Riconec/iCE40-feather/gateware/snake/snake.v

// -----------------------------------------------------------------------------
// Copyright (c) 2019 All rights reserved
// -----------------------------------------------------------------------------
// Author      : Josh Johnson <josh@joshajohnson.com>
// File        : snake.v
// Description : WIP game of snake of the LED matrix FeatherWing
// Created     : 2019-09-06 19:22:27
// Revised     : 2019-09-06 19:22:27
// Editor      : sublime text3, tab size (4)
// -----------------------------------------------------------------------------

`default_nettype none
`include "../src/debounce.v"
`include "../src/ledMatrix.v"

module top(
    input clk,
    input btn_up,
    input btn_left,
    input btn_right,
    input btn_down,
    output wire [5:0] row,
    output wire [5:0] col
);

	wire btn_up_rising, btn_left_rising, btn_right_rising, btn_down_rising;
	reg error = 0;
	reg reset_game = 1;
	reg clk_1Hz_rst = 0;

	// Matrix dimensions
	parameter DIM_X = 6;
	parameter DIM_Y = 6;

	// Mode State Machine
	parameter IDLE 	= 4'b0000;
	parameter BEGIN = 4'b0010;
	parameter PLAY 	= 4'b0100;
	parameter END 	= 4'b1000;

	reg [3:0] state = IDLE;
	reg [3:0] next_state;

	// Display control
	reg [3:0] display = 0;
	reg [2:0] countdown = 0;

	parameter START	= 4'b0000;
	parameter ONE	= 4'b0001;
	parameter TWO	= 4'b0010;
	parameter THREE	= 4'b0011;
	parameter GAME 	= 4'b0100;
	parameter DEAD 	= 4'b1000;

	// Drive state machine
	always @(*) begin
		state <= next_state;
	end

	// Mode state machine
	always @(posedge clk) begin
		case (state)
			IDLE : begin
				// Move to begin once a key is pressed
				display <= START;
				reset_game <= 0;
				clk_1Hz_rst <= 1;
				if (btn_up_rising || btn_right_rising || btn_left_rising || btn_down_rising) begin
					next_state = BEGIN;
					countdown <= 3;
				end
			end

			BEGIN : begin
				// Display 3,2,1 on screen before beginning game
				clk_1Hz_rst <= 0;
				display <= countdown;
				if (pulse_1Hz) begin
					countdown <= countdown - 1;
				end

				if (countdown == 0) begin
					next_state <= PLAY;
				end
			end

			PLAY : begin
				// Play snake util it ends
				display <= GAME;
				if (error) begin
					next_state <= END;
				end
			end

			END : begin
				// Display sad face until button pressed 
				display <= DEAD;
				if (btn_up_rising || btn_left_rising || btn_right_rising || btn_down_rising) begin
					next_state <= IDLE;
					reset_game <= 1;
				end
			end

			default: next_state <= IDLE;
		endcase
	end

	// Direction of snake
	parameter UP = 	4'b0001;
	parameter DOWN = 4'b0010;
	parameter LEFT = 4'b0100;
	parameter RIGHT = 4'b1000;

	// Initial direction of snake
	reg [3:0] direction = UP;

	// Position
	reg [2:0] pos_x = 0;
	reg [2:0] pos_y = 0;

	// Change direction after button press
	always @(posedge clk) begin
		if (reset_game) begin
			direction <= UP;
		end else if (btn_up_rising) begin
				direction <= UP;
		end else if (btn_left_rising) begin
				direction <= LEFT;
		end else if (btn_right_rising) begin
				direction <= RIGHT;
		end else if (btn_down_rising) begin
				direction <= DOWN;
		end 
	end

	// Move snake every clock cycle only if playing snake
	wire pulse_1Hz;
	always @(posedge clk) begin
		if (reset_game) begin
			error <= 1'b0;
			pos_x <= 1'b0;
			pos_y <= 1'b0;
		end else if (pulse_1Hz && (state == PLAY)) begin
			case(direction)
			UP: 	if (pos_y < DIM_Y) begin
						if (pos_y < DIM_Y - 1) begin
							pos_y <= pos_y + 1;
							error <= 1'b0;
						end else begin
							error <= 1'b1;
						end
					end 

			LEFT: 	if (pos_x >= 0) begin
						if (pos_x > 0) begin
							pos_x <= pos_x - 1;
							error <= 1'b0;
				  		end else begin
				  			error <= 1'b1;
				  		end

				  	end 

			RIGHT: 	if (pos_x < DIM_X) begin
						if (pos_x < DIM_X - 1) begin
							pos_x <= pos_x + 1;
							error <= 1'b0;
						end else begin
							error <= 1'b1;
						end
					end

			DOWN: 	if (pos_y >= 0) begin
						if (pos_y > 0) begin
							pos_y <= pos_y - 1;
							error <= 1'b0;
				  		end else begin
				  			error <= 1'b1;
				  		end

				  	end 

			default: pos_x = pos_x;
			endcase
		end
	end

	// Display image on screen
	reg [35:0] img;
	always @(posedge clk) begin
		case (display)
			START :	begin
					img [5:0] 		= 6'b000000;
					img [11:6] 		= 6'b010010;
					img [17:12] 	= 6'b000000;
					img [23:18] 	= 6'b100001;
					img [29:24] 	= 6'b011110;
					img [35:30] 	= 6'b000000;
			end 

			ONE : 	begin
					img [5:0] 		= 6'b000000;
					img [11:6] 		= 6'b011100;
					img [17:12] 	= 6'b000100;
					img [23:18] 	= 6'b000100;
					img [29:24] 	= 6'b000100;
					img [35:30] 	= 6'b011110;
			end

			TWO : 	begin
					img [5:0] 		= 6'b111100;
					img [11:6] 		= 6'b000010;
					img [17:12] 	= 6'b011100;
					img [23:18] 	= 6'b100000;
					img [29:24] 	= 6'b100000;
					img [35:30] 	= 6'b011110;
			end

			THREE : begin
					img [5:0] 		= 6'b011110;
					img [11:6] 		= 6'b000010;
					img [17:12] 	= 6'b011110;
					img [23:18] 	= 6'b000010;
					img [29:24] 	= 6'b000010;
					img [35:30] 	= 6'b011110;
			end

			GAME : begin
				img = 0;
				case (5 - pos_y)
					3'd0: img [5:0] 	= 1 << (5 - pos_x);
					3'd1: img [11:6] 	= 1 << (5 - pos_x);
					3'd2: img [17:12] 	= 1 << (5 - pos_x);
					3'd3: img [23:18] 	= 1 << (5 - pos_x);
					3'd4: img [29:24] 	= 1 << (5 - pos_x);
					3'd5: img [35:30] 	= 1 << (5 - pos_x);
					default: img 		= 36'd0;
				endcase
				end

			DEAD : begin
					img [5:0] 		= 6'b000000;
					img [11:6] 		= 6'b010010;
					img [17:12] 	= 6'b000000;
					img [23:18] 	= 6'b000000;
					img [29:24] 	= 6'b011110;
					img [35:30] 	= 6'b000000;
			end
			default : begin
					img [5:0] 		= 6'b000000;
					img [11:6] 		= 6'b000000;
					img [17:12] 	= 6'b000000;
					img [23:18] 	= 6'b000000;
					img [29:24] 	= 6'b000000;
					img [35:30] 	= 6'b000000;
			end 
		endcase
	end

	// Drive matrix
	ledMatrix inst_ledMatrix (
		.clk	(clk), 
		.img	(img), 
		.row 	(row), 
		.col 	(col)
	);

`ifdef SIMULATION
	// Increase the 1Hz clock speed
	clkDivHz #(
		.FREQUENCY(100)
	) inst_clkDivHz (
		.clk          (clk),
		.rst          (clk_1Hz_rst),
		.enable       (1'b1),
		.dividedClk   (),
		.dividedPulse (pulse_1Hz)
	);

	// pass buttons through without debounce
	assign btn_up_rising = btn_up;
	assign btn_down_rising = btn_down;
	assign btn_right_rising = btn_right;
	assign btn_left_rising = btn_left;

`else
	// 1Hz clock
	clkDivHz #(
		.FREQUENCY(1)
	) inst_clkDivHz (
		.clk          (clk),
		.rst          (clk_1Hz_rst),
		.enable       (1'b1),
		.dividedClk   (),
		.dividedPulse (pulse_1Hz)
	);

	// debonce buttons
	debounce debounce_up
	(
		.clk            (clk),
		.button         (btn_up),
		.button_db      (),
		.button_rising  (btn_up_rising),
		.button_falling ()
	);

	debounce debounce_left
	(
		.clk            (clk),
		.button         (btn_left),
		.button_db      (),
		.button_rising  (btn_left_rising),
		.button_falling ()
	);

	debounce debounce_right
	(
		.clk            (clk),
		.button         (btn_right),
		.button_db      (),
		.button_rising  (btn_right_rising),
		.button_falling ()
	);

	debounce debounce_down
	(
		.clk            (clk),
		.button         (btn_down),
		.button_db      (),
		.button_rising  (btn_down_rising),
		.button_falling ()
	);
`endif
endmodule
