Riconec/iCE40-feather/gateware/debounce/debounce.v

// Debounces an active high button, using a shift register approach. 
// This results in ~50ms of latency which is unperceivable to almost everyone.
// @input button: button to be debounced
// @output button_db: debounced button
// @output button_rising: one clock pulse upon rising edge of button_db
// @output button_falling: one clock pulse upon falling edge of button_db

`default_nettype none
`include "../src/clockDividerHertz.v"

module top(
    input clk,
    input button,
    output button_db,
    output reg button_rising,
    output reg button_falling
);

	wire dbPulse;
	reg [7:0] shiftReg = 0;
	reg [1:0] shiftRegDb = 0;
	reg [1:0] inputShift = 0;

	// dual dff to prevent metastablilty
	always @(posedge clk) begin
		inputShift[0] <= button;
		inputShift[1] <= inputShift[0];	
	end

	// generate shift reg to compare 
	always @(posedge clk) begin
		if (dbPulse) begin
			shiftReg[7:0] <= {shiftReg[6:0], inputShift[1]};
		end
	end

	// set output only if all shift reg is ones
	assign button_db = &shiftReg[7:0];
	
	// one clock pulse for rising and falling button_db
	always @(posedge clk) begin
		shiftRegDb[1:0] <= {shiftRegDb[0], button_db};

		if (shiftRegDb == 2'b01) begin
			button_rising <= 1'b1;
		end else begin
			button_rising <= 1'b0;
		end

		if (shiftRegDb == 2'b10) begin
			button_falling <= 1'b1;
		end else begin
			button_falling <= 1'b0;
		end
	end

	// clock for input sampling
	clockDividerHertz #(
			.FREQUENCY(200)
		) inst_clockDividerHz (
			.clk        	(clk),
			.rst        	(1'b0),
			.enable     	(1'b1),
			.dividedClk 	(),
			.dividedPulse	(dbPulse)
		);

endmodule
