Riconec/iCE40-feather/gateware/src/uart_rx.v

// -----------------------------------------------------------------------------
// Copyright (c) 2019 All rights reserved
// -----------------------------------------------------------------------------
// Author      : Josh Johnson <josh@joshajohnson.com>
// File        : uart_rx.v
// Description : 9600 baud uart receiver
// Created     : 2019-10-25 12:19:35
// Revised     : 2019-10-25 12:19:35
// Editor      : sublime text3, tab size (4)
// -----------------------------------------------------------------------------
`ifndef _uart_rx_v_
`define _uart_rx_v_


`default_nettype none
`include "../src/clkDivHz.v"

module uart_rx(
    input wire clk,
    input wire rst,
    input wire uart_rx,
    output wire ready,
    output wire [7:0] data
);

	localparam BAUD_RATE = 9600;
	reg [7:0] uart_data = 8'b0;
	reg uart_ready = 0;

	// UART State Machine
	localparam [3:0] IDLE 	= 4'b0000;
	localparam [3:0] START 	= 4'b0001;
	localparam [3:0] BIT0 	= 4'b0010;
	localparam [3:0] BIT1 	= 4'b0011;
	localparam [3:0] BIT2 	= 4'b0100;
	localparam [3:0] BIT3 	= 4'b0101;
	localparam [3:0] BIT4 	= 4'b0110;
	localparam [3:0] BIT5 	= 4'b0111;
	localparam [3:0] BIT6 	= 4'b1000;
	localparam [3:0] BIT7 	= 4'b1001;
	localparam [3:0] STOP 	= 4'b1010;

	reg [3:0] state = 0;
	reg [3:0] next_state = 0;

	// Drive state machine
	always @(*) begin
		state <= next_state;
	end

	// Mode state machine
	always @(posedge clk) begin
		case (state)
			IDLE : begin
				// Wait until falling edge on UART to begin
				if (uart_edge) begin
					next_state <= START;
					uart_data[7:0] <= 8'b0;
					clk_rst <= 1'b0;
					uart_ready <= 0;
				end
				
			end

			START : begin
				// Hold off half period
				if (sample_now)
					next_state <= BIT0;
			end

			BIT0 : begin
				// Sample first bit
				if (sample_now) begin
					uart_data[0] <= uart_buf[1];
					next_state <= BIT1;
				end
			end

			BIT1 : begin
				// Sample first bit
				if (sample_now) begin
					uart_data[1] <= uart_buf[1];
					next_state <= BIT2;
				end
			end

			BIT2 : begin
				// Sample first bit
				if (sample_now) begin
					uart_data[2] <= uart_buf[1];
					next_state <= BIT3;
				end
			end

			BIT3 : begin
				// Sample first bit
				if (sample_now) begin
					uart_data[3] <= uart_buf[1];
					next_state <= BIT4;
				end
			end

			BIT4 : begin
				// Sample first bit
				if (sample_now) begin
					uart_data[4] <= uart_buf[1];
					next_state <= BIT5;
				end
			end

			BIT5 : begin
				// Sample first bit
				if (sample_now) begin
					uart_data[5] <= uart_buf[1];
					next_state <= BIT6;
				end
			end

			BIT6 : begin
				// Sample first bit
				if (sample_now) begin
					uart_data[6] <= uart_buf[1];
					next_state <= BIT7;
				end
			end

			BIT7 : begin
				// Sample first bit
				if (sample_now) begin
					uart_data[7] <= uart_buf[1];
					next_state <= STOP;
				end
			end

			STOP : begin
				uart_ready <= 1'b1;
				next_state <= IDLE;
			end

			default: next_state <= IDLE;
		endcase
	end

	assign data = uart_data;
	assign ready =  uart_ready;


	// Input buffering / edge detection
	reg uart_buf [1:0];
	reg uart_edge = 0;

	always @(posedge clk) begin
		uart_buf[0] <= uart_rx;
		uart_buf[1] <= uart_buf[0];
		uart_edge <= (uart_buf[0] == 1'b0 && uart_buf[1] == 1'b1) ? 1 : 0;
	end

	// Uart Clock
	wire dividedPulse;
	reg sample_now = 0;
	reg clk_rst = 1'b1;

	clkDivHz #(
			.FREQUENCY(BAUD_RATE * 2)
		) inst_clockDividerHz (
			.clk        	(clk),
			.rst        	(clk_rst),
			.enable     	(1'b1),
			.dividedClk 	(),
			.dividedPulse	(dividedPulse)
		);

	// Generate sampling pulses
	reg counter = 1;
	always @(posedge clk) begin
		sample_now <= counter && dividedPulse; 
		if (dividedPulse) begin
			counter <= counter + 1;
		end
	end

endmodule

`endif
