Riconec/iCE40-feather/test/my_blinky/test_tb.v

/*
 *  PicoSoC - A simple example SoC using PicoRV32
 *
 *  Copyright (C) 2017  Clifford Wolf <clifford@clifford.at>
 *
 *  Permission to use, copy, modify, and/or distribute this software for any
 *  purpose with or without fee is hereby granted, provided that the above
 *  copyright notice and this permission notice appear in all copies.
 *
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
 */

`timescale 1 ns / 1 ps

module testbench;
	reg clk;
	always #5 clk = (clk === 1'b0);


	reg rst_n = 1'b0;

	initial begin
		#44 rst_n = 1'b1;
	end

	initial begin
		$dumpfile("testbench.vcd");
		$dumpvars(0, testbench);

		repeat (1) begin
			repeat (100) @(posedge clk);
			$display("+100 cycles");
		end

		$finish;
	end

	wire ledr_n, ledg_n, ledb_n, led_user;

	test #(.CLK_DIV(5)) test_inst1(clk, rst_n, ledr_n, ledg_n, ledb_n, led_user);

	
endmodule
